matei-birleanu/EbookReader/Images/Baterie.PNG

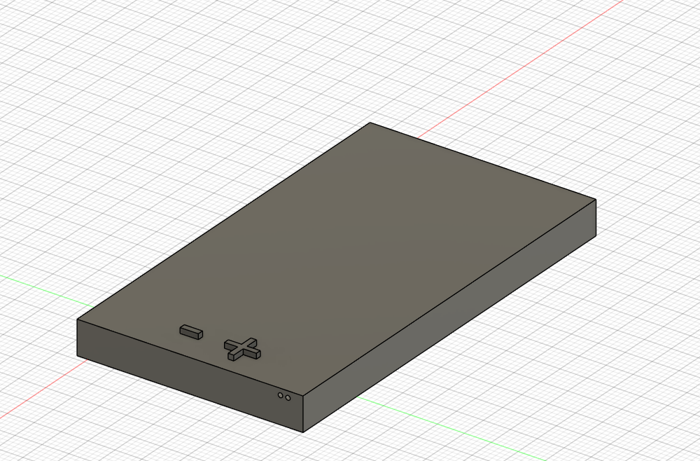
Images/Baterie.PNG
