matei-birleanu/EbookReader/Images/Capture2.PNG

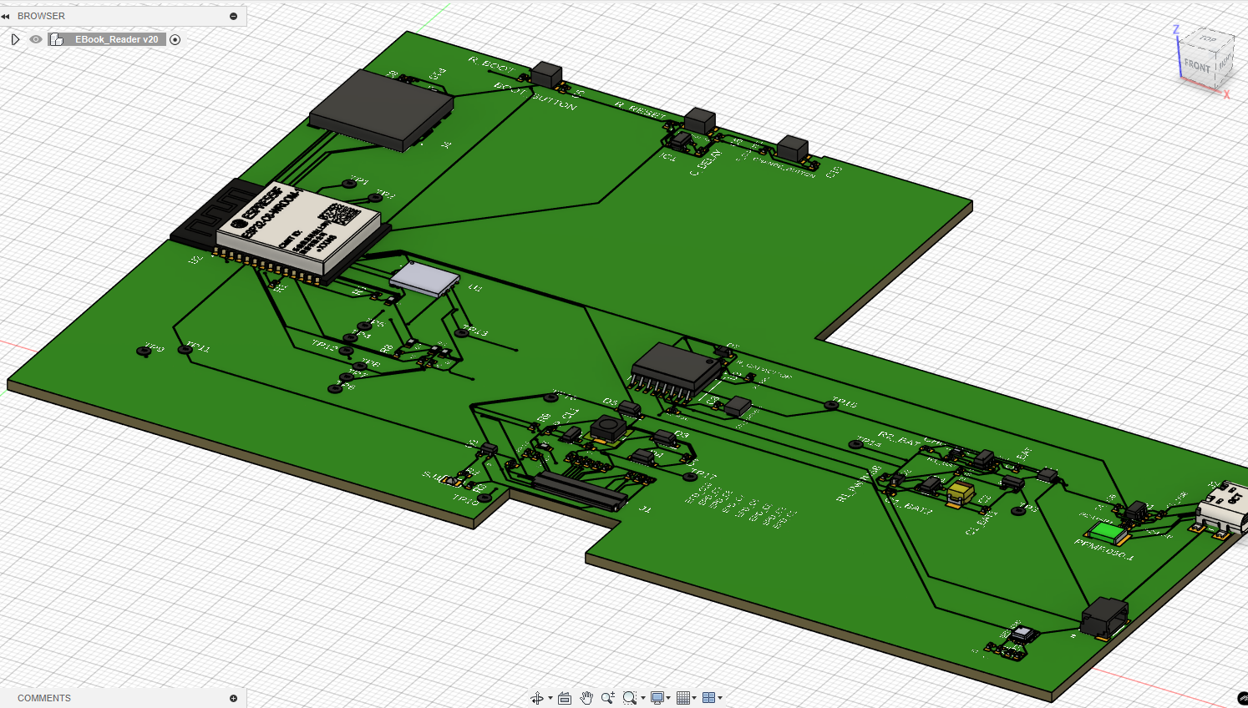
Images/Capture2.PNG
